liamlacey/Vintage-Toy-Synthesiser/Code/RPi/VintageToySynthProject/VintageSoundEngine/Maximilian/maximilian.cpp

/*
 *  maximilian.cpp
 *  platform independent synthesis library using portaudio or rtaudio
 *
 *  Created by Mick Grierson on 29/12/2009.
 *  Copyright 2009 Mick Grierson & Strangeloop Limited. All rights reserved.
 *	Thanks to the Goldsmiths Creative Computing Team.
 *	Special thanks to Arturo Castro for the PortAudio implementation.
 *
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
 */

#include "maximilian.h"
#include "math.h"

/*  Maximilian can be configured to load ogg vorbis format files using the 
*   loadOgg() method.
*   Uncomment the following to include Sean Barrett's Ogg Vorbis decoder.
*   If you're on windows, make sure to add the files std_vorbis.c and std_vorbis.h to your project*/

//#define VORBIS

#ifdef VORBIS
extern "C" {
    #include "stb_vorbis.h"
}
#endif

//This used to be important for dealing with multichannel playback
float chandiv= 1;

int maxiSettings::sampleRate = 44100;
int maxiSettings::channels = 2;
//int maxiSettings::bufferSize = 1024;
int maxiSettings::bufferSize = 128;

//this is a 514-point sinewave table that has many uses. 
double sineBuffer[514]={0,0.012268,0.024536,0.036804,0.049042,0.06131,0.073547,0.085785,0.097992,0.1102,0.12241,0.13455,0.1467,0.15884,0.17093,0.18301,0.19507,0.20709,0.21909,0.23105,0.24295,0.25485,0.26669,0.2785,0.29025,0.30197,0.31366,0.32529,0.33685,0.34839,0.35986,0.37128,0.38266,0.39395,0.40521,0.41641,0.42752,0.4386,0.44958,0.46051,0.47137,0.48215,0.49286,0.50351,0.51407,0.52457,0.53497,0.54529,0.55554,0.5657,0.57578,0.58575,0.59567,0.60547,0.6152,0.62482,0.63437,0.6438,0.65314,0.66238,0.67151,0.68057,0.68951,0.69833,0.70706,0.7157,0.72421,0.7326,0.74091,0.74908,0.75717,0.76514,0.77298,0.7807,0.7883,0.79581,0.80316,0.81042,0.81754,0.82455,0.83142,0.8382,0.84482,0.85132,0.8577,0.86392,0.87006,0.87604,0.88187,0.8876,0.89319,0.89862,0.90396,0.90912,0.91415,0.91907,0.92383,0.92847,0.93295,0.93729,0.9415,0.94556,0.94949,0.95325,0.95691,0.96039,0.96375,0.96692,0.97,0.9729,0.97565,0.97827,0.98074,0.98306,0.98523,0.98724,0.98914,0.99084,0.99243,0.99387,0.99515,0.99628,0.99725,0.99808,0.99875,0.99927,0.99966,0.99988,0.99997,0.99988,0.99966,0.99927,0.99875,0.99808,0.99725,0.99628,0.99515,0.99387,0.99243,0.99084,0.98914,0.98724,0.98523,0.98306,0.98074,0.97827,0.97565,0.9729,0.97,0.96692,0.96375,0.96039,0.95691,0.95325,0.94949,0.94556,0.9415,0.93729,0.93295,0.92847,0.92383,0.91907,0.91415,0.90912,0.90396,0.89862,0.89319,0.8876,0.88187,0.87604,0.87006,0.86392,0.8577,0.85132,0.84482,0.8382,0.83142,0.82455,0.81754,0.81042,0.80316,0.79581,0.7883,0.7807,0.77298,0.76514,0.75717,0.74908,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
	phase=phaseIn;
	
}

double maxiOsc::sinewave(double frequency) {
    //This is a sinewave oscillator
	output=sin (phase*(TWOPI));
	if ( phase >= 1.0 ) phase -= 1.0;
	phase += (1./(maxiSettings::sampleRate/(frequency)));
	return(output);
	
}

double maxiOsc::sinebuf4(double frequency) {
    //This is a sinewave oscillator that uses 4 point interpolation on a 514 point buffer
	double remainder;
	double a,b,c,d,a1,a2,a3;
	phase += 512./(maxiSettings::sampleRate/(frequency));
	if ( phase >= 511 ) phase -=512;
	remainder = phase - floor(phase);
	
	if (phase==0) {
		a=sineBuffer[(long) 512];
		b=sineBuffer[(long) phase];
		c=sineBuffer[(long) phase+1];
		d=sineBuffer[(long) phase+2];
		
	} else {
		a=sineBuffer[(long) phase-1];
		b=sineBuffer[(long) phase];
		c=sineBuffer[(long) phase+1];
		d=sineBuffer[(long) phase+2];
		
	}
	
	a1 = 0.5f * (c - a);
	a2 = a - 2.5 * b + 2.f * c - 0.5f * d;
	a3 = 0.5f * (d - a) + 1.5f * (b - c);
	output = double (((a3 * remainder + a2) * remainder + a1) * remainder + b);
	return(output);
}

double maxiOsc::sinebuf(double frequency) { //specify the frequency of the oscillator in Hz / cps etc.
    //This is a sinewave oscillator that uses linear interpolation on a 514 point buffer
	double remainder;
 	phase += 512./(maxiSettings::sampleRate/(frequency*chandiv));
	if ( phase >= 511 ) phase -=512;
	remainder = phase - floor(phase);
	output = (double) ((1-remainder) * sineBuffer[1+ (long) phase] + remainder * sineBuffer[2+(long) phase]);
	return(output);
}

double maxiOsc::coswave(double frequency) {
    //This is a cosine oscillator
	output=cos (phase*(TWOPI));
	if ( phase >= 1.0 ) phase -= 1.0;
	phase += (1./(maxiSettings::sampleRate/(frequency)));
	return(output);
	
}

double maxiOsc::phasor(double frequency) {
    //This produces a floating point linear ramp between 0 and 1 at the desired frequency 
	output=phase;
	if ( phase >= 1.0 ) phase -= 1.0;
	phase += (1./(maxiSettings::sampleRate/(frequency)));
	return(output);
} 

double maxiOsc::square(double frequency) {
    //This is a square wave
	if (phase<0.5) output=-1;
	if (phase>0.5) output=1;
	if ( phase >= 1.0 ) phase -= 1.0;
	phase += (1./(maxiSettings::sampleRate/(frequency)));
	return(output);
}

double maxiOsc::pulse(double frequency, double duty) {
    //This is a pulse generator that creates a signal between -1 and 1.
	if (duty<0.) duty=0;
	if (duty>1.) duty=1;
	if ( phase >= 1.0 ) phase -= 1.0;
	phase += (1./(maxiSettings::sampleRate/(frequency)));
	if (phase<duty) output=-1.;
	if (phase>duty) output=1.;
	return(output);
}

double maxiOsc::phasor(double frequency, double startphase, double endphase) {
    //This is a phasor that takes a value for the start and end of the ramp. 
	output=phase;
	if (phase<startphase) {
		phase=startphase;
	}
	if ( phase >= endphase ) phase = startphase;
	phase += ((endphase-startphase)/(maxiSettings::sampleRate/(frequency)));
	return(output);
}


double maxiOsc::saw(double frequency) {
	//Sawtooth generator. This is like a phasor but goes between -1 and 1
	output=phase;
	if ( phase >= 1.0 ) phase -= 2.0;
	phase += (1./(maxiSettings::sampleRate/(frequency)));
	return(output);
	
}

double maxiOsc::sawn(double frequency) {
	//Bandlimited sawtooth generator. Woohoo.
    if ( phase >= 0.5 ) phase -= 1.0;
    phase += (1./(maxiSettings::sampleRate/(frequency)));
	double temp=(8820.22/frequency)*phase;
    if (temp<-0.5) {
        temp=-0.5;
    }
    if (temp>0.5) {
        temp=0.5;
    }
    temp*=1000.0f;
    temp+=500.0f;
    double remainder = temp - floor(temp);
    output = (double) ((1.0f-remainder) * transition[(long)temp] + remainder * transition[1+(long)temp]) - phase;
	return(output);
	
}

double maxiOsc::rect(double frequency, double duty) {

    return (output);
}

double maxiOsc::triangle(double frequency) {
    //This is a triangle wave.
	if ( phase >= 1.0 ) phase -= 1.0;
	phase += (1./(maxiSettings::sampleRate/(frequency)));
	if (phase <= 0.5 ) {
		output =(phase - 0.25) * 4;
	} else {
		output =((1.0-phase) - 0.25) * 4;
	}
	return(output);
	
}

double maxiEnvelope::line(int numberofsegments,double segments[1000]) {
	//This is a basic multi-segment ramp generator that you can use for more or less anything.
    //However, it's not that intuitive.
    if (isPlaying==1) {//only make a sound once you've been triggered
	period=4./(segments[valindex+1]*0.0044);
	nextval=segments[valindex+2];
	currentval=segments[valindex];
	if (currentval-amplitude > 0.0000001 && valindex < numberofsegments) {
		amplitude += ((currentval-startval)/(maxiSettings::sampleRate/period));
	} else if (currentval-amplitude < -0.0000001 && valindex < numberofsegments) {
		amplitude -= (((currentval-startval)*(-1))/(maxiSettings::sampleRate/period));
	} else if (valindex >numberofsegments-1) {
		valindex=numberofsegments-2;
	} else {
		valindex=valindex+2;
		startval=currentval;
	}
	output=amplitude;
		
	}
	else {
		output=0;
		
	}
	return(output);
}

//and this
void maxiEnvelope::trigger(int index, double amp) {
	isPlaying=1;//ok the envelope is being used now.
	valindex=index;
	amplitude=amp;
	
}

//Delay with feedback
maxiDelayline::maxiDelayline() {
	memset( memory, 0, 88200*sizeof (double) );	
}


double maxiDelayline::dl(double input, int size, double feedback)  {
	if ( phase >=size ) {
		phase = 0;
	}
	output=memory[phase];
	memory[phase]=(memory[phase]*feedback)+(input*feedback)*0.5;
	phase+=1;
	return(output);
	
}

double maxiDelayline::dl(double input, int size, double feedback, int position)  {
	if ( phase >=size ) phase = 0;
	if ( position >=size ) position = 0;
	output=memory[position];
	memory[phase]=(memory[phase]*feedback)+(input*feedback)*chandiv;
	phase+=1;
	return(output);
	
}

//I particularly like these. cutoff between 0 and 1
double maxiFilter::lopass(double input, double cutoff) {
	output=outputs[0] + cutoff*(input-outputs[0]);
	outputs[0]=output;
	return(output);
}

//as above
double maxiFilter::hipass(double input, double cutoff) {
	output=input-(outputs[0] + cutoff*(input-outputs[0]));
	outputs[0]=output;
	return(output);
}
//awesome. cuttof is freq in hz. res is between 1 and whatever. Watch out!
double maxiFilter::lores(double input,double cutoff1, double resonance) {
	cutoff=cutoff1;
	if (cutoff<10) cutoff=10;
	if (cutoff>(maxiSettings::sampleRate)) cutoff=(maxiSettings::sampleRate);
	if (resonance<1.) resonance = 1.;
	z=cos(TWOPI*cutoff/maxiSettings::sampleRate);
	c=2-2*z;
	double r=(sqrt(2.0)*sqrt(-pow((z-1.0),3.0))+resonance*(z-1))/(resonance*(z-1));
	x=x+(input-y)*c;
	y=y+x;
	x=x*r;
	output=y;
	return(output);
}

//working hires filter
double maxiFilter::hires(double input,double cutoff1, double resonance) {
	cutoff=cutoff1;
	if (cutoff<10) cutoff=10;
	if (cutoff>(maxiSettings::sampleRate)) cutoff=(maxiSettings::sampleRate);
	if (resonance<1.) resonance = 1.;
	z=cos(TWOPI*cutoff/maxiSettings::sampleRate);
	c=2-2*z;
	double r=(sqrt(2.0)*sqrt(-pow((z-1.0),3.0))+resonance*(z-1))/(resonance*(z-1));
	x=x+(input-y)*c;
	y=y+x;
	x=x*r;
	output=input-y;
	return(output);
}

//This works a bit. Needs attention.
double maxiFilter::bandpass(double input,double cutoff1, double resonance) {
	cutoff=cutoff1;
	if (cutoff>(maxiSettings::sampleRate*0.5)) cutoff=(maxiSettings::sampleRate*0.5);
	if (resonance>=1.) resonance=0.999999;
	z=cos(TWOPI*cutoff/maxiSettings::sampleRate);
	inputs[0] = (1-resonance)*(sqrt(resonance*(resonance-4.0*pow(z,2.0)+2.0)+1));
	inputs[1] = 2*z*resonance;
	inputs[2] = pow((resonance*-1),2);
	
	output=inputs[0]*input+inputs[1]*outputs[1]+inputs[2]*outputs[2];
	outputs[2]=outputs[1];
	outputs[1]=output;
	return(output);
}

//stereo bus
double *maxiMix::stereo(double input,double two[2],double x) {
	if (x>1) x=1;
	if (x<0) x=0;
	two[0]=input*sqrt(1.0-x);
	two[1]=input*sqrt(x);
	return(two);
} 

//quad bus
double *maxiMix::quad(double input,double four[4],double x,double y) {
	if (x>1) x=1;
	if (x<0) x=0;
	if (y>1) y=1;
	if (y<0) y=0;
	four[0]=input*sqrt((1.0-x)*y);
	four[1]=input*sqrt((1.0-x)*(1.0-y));
	four[2]=input*sqrt(x*y);
	four[3]=input*sqrt(x*(1.0-y));
	return(four);
}

//ambisonic bus
double *maxiMix::ambisonic(double input,double eight[8],double x,double y,double z) {
	if (x>1) x=1;
	if (x<0) x=0;
	if (y>1) y=1;
	if (y<0) y=0;
	if (z>1) y=1;
	if (z<0) y=0;
	eight[0]=input*(sqrt((1.0-x)*y)*1.0-z);
	eight[1]=input*(sqrt((1.0-x)*(1.0-y))*1.0-z);
	eight[2]=input*(sqrt(x*y)*1.0-z);
	eight[3]=input*(sqrt(x*(1.0-y))*1.0-z);
	eight[4]=input*(sqrt((1.0-x)*y)*z);
	eight[5]=input*(sqrt((1.0-x)*(1.0-y))*z);
	eight[6]=input*sqrt((x*y)*z);
	eight[7]=input*sqrt((x*(1.0-y))*z);
	return(eight);
}

//This is the maxiSample load function. It just calls read.
bool maxiSample::load(string fileName, int channel) {
	myPath = fileName;
	readChannel=channel;
	return read();
}

// This is for OGG loading
bool maxiSample::loadOgg(string fileName, int channel) {
#ifdef VORBIS
    bool result;
	readChannel=channel;
    int channelx;
//    cout << fileName << endl;
    free(temp);
    myDataSize = stb_vorbis_decode_filename(const_cast<char*>(fileName.c_str()), &channelx, &temp);
    result = myDataSize > 0;
    printf("\nchannels = %d\nlength = %d",channelx,myDataSize);
    printf("\n");
    myChannels=(short)channelx;
    length=myDataSize;
    mySampleRate=44100;
    
    if (myChannels>1) {
        int position=0;
        int channel=readChannel;
        for (int i=channel;i<myDataSize*2;i+=myChannels) {
            temp[position]=temp[i];
            position++;
        }
    }
	return result; // this should probably be something more descriptive
#endif
    return 0;
}

//This sets the playback position to the start of a sample
void maxiSample::trigger() {
	position = 0;
    recordPosition = 0;
}

//This is the main read function.
bool maxiSample::read()
{
	bool result;
	ifstream inFile( myPath.c_str(), ios::in | ios::binary);
	result = inFile.is_open();
	if (result) {
		bool datafound = false;
		inFile.seekg(4, ios::beg);
		inFile.read( (char*) &myChunkSize, 4 ); // read the ChunkSize
		
		inFile.seekg(16, ios::beg);
		inFile.read( (char*) &mySubChunk1Size, 4 ); // read the SubChunk1Size
		
		//inFile.seekg(20, ios::beg);
		inFile.read( (char*) &myFormat, sizeof(short) ); // read the file format.  This should be 1 for PCM
		
		//inFile.seekg(22, ios::beg);
		inFile.read( (char*) &myChannels, sizeof(short) ); // read the # of channels (1 or 2)
		
		//inFile.seekg(24, ios::beg);
		inFile.read( (char*) &mySampleRate, sizeof(int) ); // read the samplerate
		
		//inFile.seekg(28, ios::beg);
		inFile.read( (char*) &myByteRate, sizeof(int) ); // read the byterate
		
		//inFile.seekg(32, ios::beg);
		inFile.read( (char*) &myBlockAlign, sizeof(short) ); // read the blockalign
		
		//inFile.seekg(34, ios::beg);
		inFile.read( (char*) &myBitsPerSample, sizeof(short) ); // read the bitspersample
		
		//ignore any extra chunks
		char chunkID[5]="";
		chunkID[4] = 0;
		int filePos = 20 + mySubChunk1Size;
		while(!datafound && !inFile.eof()) {
			inFile.seekg(filePos, ios::beg);
			inFile.read((char*) &chunkID, sizeof(char) * 4);
			inFile.seekg(filePos + 4, ios::beg);
			inFile.read( (char*) &myDataSize, sizeof(int) ); // read the size of the data
			filePos += 8;
			if (strcmp(chunkID,"data") == 0) {
				datafound = true;
			}else{
				filePos += myDataSize;
			}
		}
		
		// read the data chunk
		char * myData = (char*) malloc(myDataSize * sizeof(char));
		inFile.seekg(filePos, ios::beg);
		inFile.read(myData, myDataSize);
		length=myDataSize*(0.5/myChannels);
		inFile.close(); // close the input file
		
        cout << "Ch: " << myChannels << ", len: " << length << endl;
		if (myChannels>1) {
			int position=0;
			int channel=readChannel*2;
			for (int i=channel;i<myDataSize+6;i+=(myChannels*2)) {
				myData[position]=myData[i];
				myData[position+1]=myData[i+1];
				position+=2;
			}
		}
        free(temp);
        temp = (short*) malloc(myDataSize * sizeof(char));
        memcpy(temp, myData, myDataSize * sizeof(char));
        
        free(myData);
		
	}else {
//		cout << "ERROR: Could not load sample: " <<myPath << endl; //This line seems to be hated by windows 
        printf("ERROR: Could not load sample.");

	}
	
	
	return result; // this should probably be something more descriptive
}

//This plays back at the correct speed. Always loops.
double maxiSample::play() {
	position++;
	if ((long) position >= length) position=0;
	output = (double) temp[(long)position]/32767.0;
	return output;
}

void maxiSample::setPosition(double newPos) {
    position = maxiMap::clamp<double>(newPos, 0.0, 1.0) * length;
}

//start end and points are between 0 and 1
double maxiSample::playLoop(double start, double end) {
    position++;
    if (position < length * start) position = length * start;
    if ((long) position >= length * end) position = length * start;
    output = (double) temp[(long)position]/32767.0;
    return output;
}

double maxiSample::playUntil(double end) {
    position++;
    if ((long) position<length * end)
        output = (double) temp[(long)position]/32767.0;
    else {
        output=0;
    }
    return output;
}


//This plays back at the correct speed. Only plays once. To retrigger, you have to manually reset the position
double maxiSample::playOnce() {
	position++;
	if ((long) position<length)
        output = (double) temp[(long)position]/32767.0;
    else {
        output=0;
    }
	return output;

}

//Same as above but takes a speed value specified as a ratio, with 1.0 as original speed
double maxiSample::playOnce(double speed) {
	position=position+((speed*chandiv)/(maxiSettings::sampleRate/mySampleRate));
	double remainder = position - (long) position;
	if ((long) position<length)
		output = (double) ((1-remainder) * temp[1+ (long) position] + remainder * temp[2+(long) position])/32767;//linear interpolation
	else 
		output=0;
	return(output);
}

//As above but looping
double maxiSample::play(double speed) {
	double remainder;
	long a,b;
	position=position+((speed*chandiv)/(maxiSettings::sampleRate/mySampleRate));
	if (speed >=0) {
		
		if ((long) position>=length-1) position=1;
		remainder = position - floor(position);
		if (position+1<length) {
			a=position+1;
			
		}
		else {
			a=length-1;
		}
		if (position+2<length)
		{
		b=position+2;
		}
		else {
		b=length-1;
		}
		
		output = (double) ((1-remainder) * temp[a] + remainder * temp[b])/32767;//linear interpolation
} else {
		if ((long) position<0) position=length;
		remainder = position - floor(position);
		if (position-1>=0) {
			a=position-1;
				
			}
			else {
				a=0;
			}
	if (position-2>=0) {
		b=position-2;
			}
			else {
				b=0;
			}
		output = (double) ((-1-remainder) * temp[a] + remainder * temp[b])/32767;//linear interpolation
	}	
	return(output);
}

//placeholder
double maxiSample::play(double frequency, double start, double end) {
	return play(frequency, start, end, position);
}

//This allows you to say how often a second you want a specific chunk of audio to play
double maxiSample::play(double frequency, double start, double end, double &pos) {
	double remainder;
	if (end>=length) end=length-1;
	long a,b;

	if (frequency >0.) {
		if (pos<start) {
			pos=start;
		}
		
		if ( pos >= end ) pos = start;
		pos += ((end-start)/((maxiSettings::sampleRate)/(frequency*chandiv)));
		remainder = pos - floor(pos);
		long posl = floor(pos);
		if (posl+1<length) {
			a=posl+1;
			
		}
		else {
			a=posl-1;
		}
		if (posl+2<length) {
			b=posl+2;
		}
		else {
			b=length-1;
		}

		output = (double) ((1-remainder) * temp[a] +
						   remainder * temp[b])/32767;//linear interpolation
	} else {
		frequency*=-1.;
		if ( pos <= start ) pos = end;
		pos -= ((end-start)/(maxiSettings::sampleRate/(frequency*chandiv)));
		remainder = pos - floor(pos);
		long posl = floor(pos);
		if (posl-1>=0) {
			a=posl-1;
		}
		else {
			a=0;
		}
		if (posl-2>=0) {
			b=posl-2;
		}
		else {
			b=0;
		}		
		output = (double) ((-1-remainder) * temp[a] +
						   remainder * temp[b])/32767;//linear interpolation
		
	}
	
	return(output);
}


//Same as above. better cubic inerpolation. Cobbled together from various (pd externals, yehar, other places).
double maxiSample::play4(double frequency, double start, double end) {
	double remainder;
	double a,b,c,d,a1,a2,a3;
	if (frequency >0.) {
		if (position<start) {
			position=start;
		}
		if ( position >= end ) position = start;
		position += ((end-start)/(maxiSettings::sampleRate/(frequency*chandiv)));
		remainder = position - floor(position);
		if (position>0) {
			a=temp[(int)(floor(position))-1];

		} else {
			a=temp[0];
			
		}
		
		b=temp[(long) position];
		if (position<end-2) {
			c=temp[(long) position+1];

		} else {
			c=temp[0];

		}
		if (position<end-3) {
			d=temp[(long) position+2];

		} else {
			d=temp[0];
		}
		a1 = 0.5f * (c - a);
		a2 = a - 2.5 * b + 2.f * c - 0.5f * d;
		a3 = 0.5f * (d - a) + 1.5f * (b - c);
		output = (double) (((a3 * remainder + a2) * remainder + a1) * remainder + b) / 32767;
		
	} else {
        frequency*=-1.;
		if ( position <= start ) position = end;
		position -= ((end-start)/(maxiSettings::sampleRate/(frequency*chandiv)));
		remainder = position - floor(position);
		if (position>start && position < end-1) {
			a=temp[(long) position+1];
			
		} else {
			a=temp[0];
			
		}
		
		b=temp[(long) position];
		if (position>start) {
			c=temp[(long) position-1];
			
		} else {
			c=temp[0];
			
		}
		if (position>start+1) {
			d=temp[(long) position-2];
			
		} else {
			d=temp[0];
		}
		a1 = 0.5f * (c - a);
		a2 = a - 2.5 * b + 2.f * c - 0.5f * d;
		a3 = 0.5f * (d - a) + 1.5f * (b - c);
		output = (double) (((a3 * remainder + a2) * -remainder + a1) * -remainder + b) / 32767;
		
	}
	
	return(output);
}


//You don't need to worry about this stuff.
double maxiSample::bufferPlay(unsigned char &bufferin,long length) {
	double remainder;
	short* buffer = (short *)&bufferin;
	position=(position+1);
	remainder = position - (long) position;
	if ((long) position>length) position=0;
	output = (double) ((1-remainder) * buffer[1+ (long) position] + remainder * buffer[2+(long) position])/32767;//linear interpolation
	return(output);
}

double maxiSample::bufferPlay(unsigned char &bufferin,double speed,long length) {
	double remainder;
	long a,b;
	short* buffer = (short *)&bufferin;
	position=position+((speed*chandiv)/(maxiSettings::sampleRate/mySampleRate));
	if (speed >=0) {
		
		if ((long) position>=length-1) position=1;
		remainder = position - floor(position);
		if (position+1<length) {
			a=position+1;
			
		}
		else {
			a=length-1;
		}
		if (position+2<length)
		{
			b=position+2;
		}
		else {
			b=length-1;
		}
		
		output = (double) ((1-remainder) * buffer[a] + remainder * buffer[b])/32767;//linear interpolation
	} else {
		if ((long) position<0) position=length;
		remainder = position - floor(position);
		if (position-1>=0) {
			a=position-1;
			
		}
		else {
			a=0;
		}
		if (position-2>=0) {
			b=position-2;
		}
		else {
			b=0;
		}
		output = (double) ((-1-remainder) * buffer[a] + remainder * buffer[b])/32767;//linear interpolation
	}	
	return(output);
}

double maxiSample::bufferPlay(unsigned char &bufferin,double frequency, double start, double end) {
	double remainder;
	length=end;
	long a,b;
	short* buffer = (short *)&bufferin;
	if (frequency >0.) {
		if (position<start) {
			position=start;
		}
		
		if ( position >= end ) position = start;
		position += ((end-start)/(maxiSettings::sampleRate/(frequency*chandiv)));
		remainder = position - floor(position);
		long pos = floor(position);
		if (pos+1<length) {
			a=pos+1;
			
		}
		else {
			a=pos-1;
		}
		if (pos+2<length) {
			b=pos+2;
		}
		else {
			b=length-1;
		}
		
		output = (double) ((1-remainder) * buffer[a] +
						   remainder * buffer[b])/32767;//linear interpolation
	} else {
        frequency*=-1.;
		if ( position <= start ) position = end;
		position -= ((end-start)/(maxiSettings::sampleRate/(frequency*chandiv)));
		remainder = position - floor(position);
		long pos = floor(position);
		if (pos-1>=0) {
			a=pos-1;
		}
		else {
			a=0;
		}
		if (pos-2>=0) {
			b=pos-2;
		}
		else {
			b=0;
		}		
		output = (double) ((-1-remainder) * buffer[a] +
						   remainder * buffer[b])/32767;//linear interpolation
		
	}
	
	return(output);
}

//better cubic inerpolation. Cobbled together from various (pd externals, yehar, other places).
double maxiSample::bufferPlay4(unsigned char &bufferin,double frequency, double start, double end) {
	double remainder;
	double a,b,c,d,a1,a2,a3;
	short* buffer = (short*)&bufferin;
	if (frequency >0.) {
		if (position<start) {
			position=start;
		}
		if ( position >= end ) position = start;
		position += ((end-start)/(maxiSettings::sampleRate/(frequency*chandiv)));
		remainder = position - floor(position);
		if (position>0) {
			a=buffer[(int)(floor(position))-1];
			
		} else {
			a=buffer[0];
			
		}
		
		b=buffer[(long) position];
		if (position<end-2) {
			c=buffer[(long) position+1];
			
		} else {
			c=buffer[0];
			
		}
		if (position<end-3) {
			d=buffer[(long) position+2];
			
		} else {
			d=buffer[0];
		}
		a1 = 0.5f * (c - a);
		a2 = a - 2.5 * b + 2.f * c - 0.5f * d;
		a3 = 0.5f * (d - a) + 1.5f * (b - c);
		output = (double) (((a3 * remainder + a2) * remainder + a1) * remainder + b) / 32767;
		
	} else {
        frequency*=-1.;
		if ( position <= start ) position = end;
		position -= ((end-start)/(maxiSettings::sampleRate/(frequency*chandiv)));
		remainder = position - floor(position);
		if (position>start && position < end-1) {
			a=buffer[(long) position+1];
			
		} else {
			a=buffer[0];
			
		}
		
		b=buffer[(long) position];
		if (position>start) {
			c=buffer[(long) position-1];
			
		} else {
			c=buffer[0];
			
		}
		if (position>start+1) {
			d=buffer[(long) position-2];
			
		} else {
			d=buffer[0];
		}
		a1 = 0.5f * (c - a);
		a2 = a - 2.5 * b + 2.f * c - 0.5f * d;
		a3 = 0.5f * (d - a) + 1.5f * (b - c);
		output = (double) (((a3 * remainder + a2) * -remainder + a1) * -remainder + b) / 32767;
		
	}
	
	return(output);
}


void maxiSample::getLength() {
	length=myDataSize*0.5;
}

void maxiSample::setLength(unsigned long numSamples) {
    cout << "Length: " << numSamples << endl;
    short *newData = (short*) malloc(sizeof(short) * numSamples);
    if (NULL!=temp) {
        unsigned long copyLength = min((unsigned long)length, numSamples);
        memcpy(newData, temp, sizeof(short) * copyLength);
    }
    temp = newData;
    myDataSize = numSamples * 2;
    length=numSamples;
    position=0;
    recordPosition=0;
}

void maxiSample::clear() {
    memset(temp, 0, myDataSize);
}

void maxiSample::reset() {
    position=0;
}

void maxiSample::normalise(float maxLevel) {
    short maxValue = 0;
    for(int i=0; i < length; i++) {
        if (abs(temp[i]) > maxValue) {
            maxValue = abs(temp[i]);
        }
    }
    float scale = 32767.0 * maxLevel / (float) maxValue;
    for(int i=0; i < length; i++) {
        temp[i] = round(scale * (float) temp[i]);
    }
}

void maxiSample::autoTrim(float alpha, float threshold, bool trimStart, bool trimEnd) {
    
    int startMarker=0;
    if(trimStart) {
        maxiLagExp<float> startLag(alpha, 0);
        while(startMarker < length) {
            startLag.addSample(abs(temp[startMarker]));
            if (startLag.value() > threshold) {
                break;
            }
            startMarker++;
        }
    }
    
    int endMarker = length-1;
    if(trimEnd) {
        maxiLagExp<float> endLag(alpha, 0);
        while(endMarker > 0) {
            endLag.addSample(abs(temp[endMarker]));
            if (endLag.value() > threshold) {
                break;
            }
            endMarker--;
        }
    }
    
    cout << "Autotrim: start: " << startMarker << ", end: " << endMarker << endl;
    
    int newLength = endMarker - startMarker;
    if (newLength > 0) {
        short *newData = (short*) malloc(sizeof(short) * newLength);
        for(int i=0; i < newLength; i++) {
            newData[i] = temp[i+startMarker];
        }
        free(temp);
        temp = newData;
        myDataSize = newLength * 2;
        length=newLength;
        position=0;
        recordPosition=0;
        //envelope the start
        int fadeSize=min((long)100, length);
        for(int i=0; i < fadeSize; i++) {
            float factor = i / (float) fadeSize;
            temp[i] = round(temp[i] * factor);
            temp[length - 1 - i] = round(temp[length - 1 - i] * factor);
        }
    }
}





/* OK this compressor and gate are now ready to use. The envelopes, like all the envelopes in this recent update, use stupid algorithms for 
 incrementing - consequently a long attack is something like 0.0001 and a long release is like 0.9999.
 Annoyingly, a short attack is 0.1, and a short release is 0.99. I'll sort this out laters */

double maxiDyn::gate(double input, double threshold, long holdtime, double attack, double release) {
	
	if (fabs(input)>threshold && attackphase!=1){ 
		holdcount=0;
		releasephase=0;
		attackphase=1;
		if(amplitude==0) amplitude=0.01;
	}
	
	if (attackphase==1 && amplitude<1) {
		amplitude*=(1+attack);
		output=input*amplitude;
	}
	
	if (amplitude>=1) {
		attackphase=0;
		holdphase=1;
	}
	
	if (holdcount<holdtime && holdphase==1) {
		output=input;
		holdcount++;
	}
	
	if (holdcount==holdtime) {
		holdphase=0;
		releasephase=1;
	}
	
	if (releasephase==1 && amplitude>0.) {
		output=input*(amplitude*=release);
		
	}
	
	return output;
}


double maxiDyn::compressor(double input, double ratio, double threshold, double attack, double release) {
	
	if (fabs(input)>threshold && attackphase!=1){ 
		holdcount=0;
		releasephase=0;
		attackphase=1;
		if(currentRatio==0) currentRatio=ratio;
	}
	
	if (attackphase==1 && currentRatio<ratio-1) {
		currentRatio*=(1+attack);
	}
	
	if (currentRatio>=ratio-1) {
		attackphase=0;
		releasephase=1;
	}
	
	if (releasephase==1 && currentRatio>0.) {
		currentRatio*=release;		
	}
	
	if (input>0.) {
		output = input/(1.+currentRatio);
	} else {
		output = input/(1.+currentRatio);
	}
	
	return output*(1+log(ratio));
}

double maxiDyn::compress(double input) {
    
    if (fabs(input)>threshold && attackphase!=1){
        holdcount=0;
        releasephase=0;
        attackphase=1;
        if(currentRatio==0) currentRatio=ratio;
    }
    
    if (attackphase==1 && currentRatio<ratio-1) {
        currentRatio*=(1+attack);
    }
    
    if (currentRatio>=ratio-1) {
        attackphase=0;
        releasephase=1;
    }
    
    if (releasephase==1 && currentRatio>0.) {
        currentRatio*=release;
    }
    
    if (input>0.) {
        output = input/(1.+currentRatio);
    } else {
        output = input/(1.+currentRatio);
    }
    
    return output*(1+log(ratio));
}


//ltml - added by me
maxiEnv::maxiEnv()
{
    holdtime = 1;
}

/* Lots of people struggle with the envelope generators so here's a new easy one.
 It takes mental numbers for attack and release tho. Basically, they're exponentials.
 I'll map them out later so that it's a bit more intuitive */
double maxiEnv::ar(double input, double attack, double release, long holdtime, int trigger) {
	
	if (trigger==1 && attackphase!=1 && holdphase!=1){ 
		holdcount=0;
		releasephase=0;
		attackphase=1;
	}
	
	if (attackphase==1) {
		amplitude+=(1*attack);
		output=input*amplitude;
	}
	
	if (amplitude>=1) {
		amplitude=1;
		attackphase=0;
		holdphase=1;
	}
	
	if (holdcount<holdtime && holdphase==1) {
		output=input;
		holdcount++;
	}
	
	if (holdcount==holdtime && trigger==1) {
		output=input;
	}
	
	if (holdcount==holdtime && trigger!=1) {
		holdphase=0;
		releasephase=1;
	}
	
	if (releasephase==1 && amplitude>0.) {
		output=input*(amplitude*=release);
		
	}
	
	return output;
}

/* adsr. It's not bad, very simple to use*/

double maxiEnv::adsr(double input, double attack, double decay, double sustain, double release, long holdtime, int trigger) {
    
    if (trigger==1 && attackphase!=1 && holdphase!=1 && decayphase!=1){
        holdcount=0;
        decayphase=0;
        sustainphase=0;
        releasephase=0;
        attackphase=1;
    }
    
    if (attackphase==1) {
        releasephase=0;
        amplitude+=(1*attack);
        output=input*amplitude;
        
        if (amplitude>=1) {
            amplitude=1;
            attackphase=0;
            decayphase=1;
        }
    }
    
    
    if (decayphase==1) {
        output=input*(amplitude*=decay);
        if (amplitude<=sustain) {
            decayphase=0;
            holdphase=1;
        }
    }
    
    if (holdcount<holdtime && holdphase==1) {
        output=input*amplitude;
        holdcount++;
    }
    
    if (holdcount>=holdtime && trigger==1) {
        output=input*amplitude;
    }
    
    if (holdcount>=holdtime && trigger!=1) {
        holdphase=0;
        releasephase=1;
    }
    
    if (releasephase==1 && amplitude>0.) {
        output=input*(amplitude*=release);
        
    }
    
    return output;
}

double maxiEnv::adsr(double input, int trigger)
{
    //if get a trigger value of 1 while in no phase or the release phase
    if (trigger == 1 && attackphase != 1 && sustainphase != 1 && decayphase != 1)
    {
        //reset variables and start the attack phase
        decayphase = 0;
        sustainphase = 0;
        releasephase = 0;
        attackphase = 1;
    }
    
    //if get a trigger value of 0 while in the attack, decay, or sustain ohase
    else if (trigger == 0 && (attackphase == 1 || decayphase == 1 || sustainphase == 1))
    {
        //start the release phase
        attackphase = 0;
        decayphase = 0;
        sustainphase = 0;
        releasephase = 1;
    }
    
    //if in the attack phase
    if (attackphase == 1 && trigger == 1)
    {
        //increment the output value
        amplitude += (1 * attack);
        output = input * amplitude;
        
        //if reached the end of the attack phase
        if (amplitude >= 1)
        {
            amplitude = 1;
            attackphase = 0;
            
            //if we have a decay time
            if (decay > 0)
            {
                //start the decay phase
                decayphase = 1;
            }
            //if decay time is set to 0
            else
            {
                //start the sustain phase
                amplitude = sustain;
                sustainphase = 1;
            }
            
        } //if (amplitude >= 1)
        
    } //if (attackphase == 1 && trigger == 1)
    
    //if in the decay phase
    if (decayphase == 1 && trigger == 1)
    {
        //increment the output value
        output = input * (amplitude *= decay);
        
        //if reached the start of the sustain phase
        if (amplitude <= sustain)
        {
            //start the sustain phase
            decayphase = 0;
            sustainphase = 1;
        }
    }
    
    //if in the sustain phase
    if (sustainphase == 1 && trigger == 1)
    {
        //keep the output value at the sustain value
        output = input * amplitude;
    }
    
    //if in the release phase
    if (releasephase == 1 && amplitude > 0.)
    {
        //increment the output value
        output = input * (amplitude *= release);
    }
    
    return output;
    
    
//    if (trigger==1 && attackphase!=1 && holdphase!=1 && decayphase!=1){
//        holdcount=0;
//        decayphase=0;
//        sustainphase=0;
//        releasephase=0;
//        attackphase=1;
//    }
//    
//    if (attackphase==1) {
//        releasephase=0;
//        amplitude+=(1*attack);
//        output=input*amplitude;
//        
//        if (amplitude>=1) {
//            amplitude=1;
//            attackphase=0;
//            decayphase=1;
//        }
//    }
//    
//    
//    if (decayphase==1) {
//        output=input*(amplitude*=decay);
//        if (amplitude<=sustain) {
//            decayphase=0;
//            holdphase=1;
//        }
//    }
//    
//    if (holdcount<holdtime && holdphase==1) {
//        output=input*amplitude;
//        holdcount++;
//    }
//    
//    if (holdcount>=holdtime && trigger==1) {
//        output=input*amplitude;
//    }
//    
//    if (holdcount>=holdtime && trigger!=1) {
//        holdphase=0;
//        releasephase=1;
//    }
//    
//    if (releasephase==1 && amplitude>0.) {
//        output=input*(amplitude*=release);
//        
//    }
//    
//    return output;
}


void maxiEnv::setAttack(double attackMS) {
    attack = 1-pow( 0.01, 1.0 / ( attackMS * maxiSettings::sampleRate * 0.001 ) );
}

void maxiEnv::setRelease(double releaseMS) {
    release = pow( 0.01, 1.0 / ( releaseMS * maxiSettings::sampleRate * 0.001 ) );
}

void maxiEnv::setSustain(double sustainL) {
    sustain = sustainL;
}

void maxiEnv::setDecay(double decayMS) {
    decay = pow( 0.01, 1.0 / ( decayMS * maxiSettings::sampleRate * 0.001 ) );
}

void maxiDyn::setAttack(double attackMS) {
    attack = pow( 0.01, 1.0 / ( attackMS * maxiSettings::sampleRate * 0.001 ) );
}

void maxiDyn::setRelease(double releaseMS) {
    release = pow( 0.01, 1.0 / ( releaseMS * maxiSettings::sampleRate * 0.001 ) );
}

void maxiDyn::setThreshold(double thresholdI) {
    threshold = thresholdI;
}

void maxiDyn::setRatio(double ratioF) {
    ratio = ratioF;
}


double convert::mtof(int midinote) {
	
	return mtofarray[midinote];
}


template<> void maxiEnvelopeFollower::setAttack(double attackMS) {
    attack = pow( 0.01, 1.0 / ( attackMS * maxiSettings::sampleRate * 0.001 ) );
}

template<> void maxiEnvelopeFollower::setRelease(double releaseMS) {
    release = pow( 0.01, 1.0 / ( releaseMS * maxiSettings::sampleRate * 0.001 ) );    
}

double pitchRatios[256]= {0.0006517771980725,0.0006905338959768,0.0007315951515920, 0.0007750981021672, 0.0008211878011934, 0.0008700182079338, 0.0009217521874234, 0.0009765623835847, 0.0010346318595111, 0.0010961542138830, 0.0011613349197432, 0.0012303915573284, 0.0013035543961450, 0.0013810677919537, 0.0014631903031841, 0.0015501962043345, 0.0016423756023869, 0.0017400364158675, 0.0018435043748468, 0.0019531247671694, 0.0020692637190223, 0.0021923084277660, 0.0023226698394865, 0.0024607831146568, 0.0026071087922901, 0.0027621355839074, 0.0029263808391988, 0.0031003924086690, 0.0032847514376044, 0.0034800728317350, 0.0036870087496936, 0.0039062497671694, 0.0041385274380445, 0.0043846168555319, 0.0046453396789730, 0.0049215662293136, 0.0052142175845802, 0.0055242711678147, 0.0058527616783977, 0.0062007848173380, 0.0065695028752089, 0.0069601456634700, 0.0073740174993873, 0.0078124995343387, 0.0082770548760891, 0.0087692337110639, 0.0092906802892685, 0.0098431324586272, 0.0104284351691604, 0.0110485423356295, 0.0117055233567953, 0.0124015696346760, 0.0131390057504177, 0.0139202913269401, 0.0147480349987745, 0.0156249990686774, 0.0165541097521782, 0.0175384692847729, 0.0185813605785370, 0.0196862649172544, 0.0208568722009659, 0.0220970865339041, 0.0234110467135906, 0.0248031392693520, 0.0262780115008354, 0.0278405826538801, 0.0294960699975491, 0.0312499981373549, 0.0331082195043564, 0.0350769385695457, 0.0371627211570740, 0.0393725298345089, 0.0417137444019318, 0.04419417306780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
    inverse = false;
    gain = 1;
    
    maxiKick::envelope.setAttack(0);
    maxiKick::setPitch(200);
    maxiKick::envelope.setDecay(1);
    maxiKick::envelope.setSustain(1);
    maxiKick::envelope.setRelease(500);
    maxiKick::envelope.holdtime=1;
    maxiKick::envelope.trigger=0;
    
};

double maxiKick::play(){
    
    envOut=envelope.adsr(1.,envelope.trigger);
    
    if (inverse) {
        
        envOut=fabs(1-envOut);
        
    }
    
    output=kick.sinewave(pitch*envOut)*envOut;
    
    if (envelope.trigger==1) {
        envelope.trigger=0;
    }
    
    if (useDistortion) {
        
        output=distort.fastAtanDist(output, distortion);
    }
    
    if (useFilter) {
        
        output=filter.lores(output, cutoff, resonance);
        
    }
    
    if (useLimiter) {
        
        if (output*gain > 1) {
            
            return 1.;
            
        } else if (output*gain < -1) {
            
            return -1.;
            
        } else {
            
            return output*gain;
            
        }
        
        
        
    } else {
        
        return output*gain;
        
    }
};

void maxiKick::setRelease(double release) {
    
    envelope.setRelease(release);
    
}

void maxiKick::setPitch(double newPitch) {
    
    pitch=newPitch;
    
}

void maxiKick::trigger() {
    
    envelope.trigger=1;
    
}

maxiSnare::maxiSnare()
{
    output = 0;
    outputD = 0;
    useDistortion = false;
    useLimiter = false;
    useFilter = true;
    distortion = 0;
    inverse = false;
    gain = 1;
    
    maxiSnare::envelope.setAttack(0);
    maxiSnare::setPitch(800);
    maxiSnare::envelope.setDecay(20);
    maxiSnare::envelope.setSustain(0.05);
    maxiSnare::envelope.setRelease(300);
    maxiSnare::envelope.holdtime=1;
    maxiSnare::envelope.trigger=0;
    
};

double maxiSnare::play(){
    
    envOut=envelope.adsr(1.,envelope.trigger);
    
    if (inverse) {
        
        envOut=fabs(1-envOut);
        
    }
    
    output=(tone.triangle(pitch*(0.1+(envOut*0.85)))+noise.noise())*envOut;
    
    if (envelope.trigger==1) {
        envelope.trigger=0;
    }
    
    if (useDistortion) {
        
        output=distort.fastAtanDist(output, distortion);
    }
    
    if (useFilter) {
        
        output=filter.lores(output, cutoff, resonance);
        
    }
    
    if (useLimiter) {
        
        if (output*gain > 1) {
            
            return 1.;
            
        } else if (output*gain < -1) {
            
            return -1.;
            
        } else {
            
            return output*gain;
            
        }
        
        
        
    } else {
        
        return output*gain;
        
    }
    
};

void maxiSnare::setRelease(double release) {
    
    envelope.setRelease(release);
    
}

void maxiSnare::setPitch(double newPitch) {
    
    pitch=newPitch;
    
}

void maxiSnare::trigger() {
    
    envelope.trigger=1;
    
}

maxiHats::maxiHats()
{
    output = 0;
    outputD = 0;
    useDistortion = false;
    useLimiter = false;
    useFilter = false;
    distortion = 0;
    inverse = false;
    gain = 1;
    
    maxiHats::envelope.setAttack(0);
    maxiHats::setPitch(12000);
    maxiHats::envelope.setDecay(20);
    maxiHats::envelope.setSustain(0.1);
    maxiHats::envelope.setRelease(300);
    maxiHats::envelope.holdtime=1;
    maxiHats::envelope.trigger=0;
    maxiHats::filter.setCutoff(8000);
    maxiHats::filter.setResonance(1);
    
};

double maxiHats::play(){
    
    envOut=envelope.adsr(1.,envelope.trigger);
    
    if (inverse) {
        
        envOut=fabs(1-envOut);
        
    }
    
    output=(tone.sinebuf(pitch)+noise.noise())*envOut;
    
    if (envelope.trigger==1) {
        envelope.trigger=0;
    }
    
    if (useDistortion) {
        
        output=distort.fastAtanDist(output, distortion);
    }
    
    if (useFilter) {
        
        output=filter.play(output, 0., 0., 1., 0.);
        
    }
    
    if (useLimiter) {
        
        if (output*gain > 1) {
            
            return 1.;
            
        } else if (output*gain < -1) {
            
            return -1.;
            
        } else {
            
            return output*gain;
            
        }
        
        
        
    } else {
        
        return output*gain;
        
    }
    
};

void maxiHats::setRelease(double release) {
    
    envelope.setRelease(release);
    
}

void maxiHats::setPitch(double newPitch) {
    
    pitch=newPitch;
    
}

void maxiHats::trigger() {
    
    envelope.trigger=1;
    
}



maxiClock::maxiClock() {
    
    playHead=0;
    currentCount=0;
    lastCount=0;
    bpm=120;
    ticks=1;
    maxiClock::setTempo(bpm);
    
}


void maxiClock::ticker() {
    
    tick=false;
    currentCount=floor(timer.phasor(bps));//this sets up a metronome that ticks n times a second
    
    if (lastCount!=currentCount) {//if we have a new timer int this sample,
        
        tick=true;
        playHead++;//iterate the playhead
        
    }
    
}


void maxiClock::setTempo(double bpmIn) {
    
    bpm=bpmIn;
    bps=(bpm/60.)*ticks;
}


void maxiClock::setTicksPerBeat(int ticksPerBeat) {
    
    ticks=ticksPerBeat;
    maxiClock::setTempo(bpm);
    
}

maxiSampler::maxiSampler()
{
    originalPitch=67;
    outputD = 0;
    useDistortion = false;
    useLimiter = false;
    useFilter = false;
    distortion = 0;
    inverse = false;
    gain = 1;
    currentVoice=0;
    sustain = true;

    maxiSampler::voices=32;
    maxiSampler::currentVoice=0;
    
    for (int i=0;i<voices;i++) {
        
        maxiSampler::envelopes[i].setAttack(0);
        maxiSampler::envelopes[i].setDecay(1);
        maxiSampler::envelopes[i].setSustain(1.);
        maxiSampler::envelopes[i].setRelease(2000);
        maxiSampler::envelopes[i].holdtime=1;
        maxiSampler::envelopes[i].trigger=0;
        maxiSampler::envOut[i]=0;
        maxiSampler::pitch[i]=0;
        maxiSampler::outputs[i]=0;
        
        
    }
}

void maxiSampler::setNumVoices(int numVoices) {
    
    voices=numVoices;
    
}

double maxiSampler::play() {
    
    output=0;
    
    for (int i=0;i<voices;i++) {
        
        envOut[i]=envelopes[i].adsr(envOutGain[i],envelopes[i].trigger);
        
        if (envOut[i]>0.) {
            outputs[i]=samples[i].play(pitchRatios[(int)pitch[i]+originalPitch]*((1./samples[i].length)*maxiSettings::sampleRate),0,samples[i].length)*envOut[i];
            output+=outputs[i]/voices;
            
            if (envelopes[i].trigger==1 && !sustain) {
                envelopes[i].trigger=0;
                
            }
            
        }
        
    } return output;
    
}

void maxiSampler::load(string inFile, bool setall) {
    
    if (setall) {
        for (int i=0;i<voices;i++) {
            
            samples[i].load(inFile);
            
        }
        
    } else {
        
        samples[currentVoice].load(inFile);
        
    }
    
    
}

void maxiSampler::setPitch(double pitchIn, bool setall) {
    
    if (setall) {
        for (int i=0;i<voices;i++) {
            
            pitch[i]=pitchIn;
            
        }
        
    } else {
        
        pitch[currentVoice]=pitchIn;
        
    }
    
}

void maxiSampler::midiNoteOn(double pitchIn, double velocity, bool setall) {
    
    if (setall) {
        for (int i=0;i<voices;i++) {
            
            pitch[i]=pitchIn;
            
        }
        
    } else {
        
        pitch[currentVoice]=pitchIn;
        envOutGain[currentVoice]=velocity/128;
        
    }
    
}

void maxiSampler::midiNoteOff(double pitchIn, double velocity, bool setall) {
    
    
    for (int i=0;i<voices;i++){
        
        if (pitch[i]==pitchIn) {
            
            envelopes[i].trigger=0;
            
        }
        
    }
}


void maxiSampler::setAttack(double attackD, bool setall) {
    
    if (setall) {
        
        for (int i=0;i<voices;i++) {
            
            envelopes[i].setAttack(attackD);
            
        }
        
    } else {
        
        envelopes[currentVoice].setAttack(attackD);
        
        
    }
    
    
}

void maxiSampler::setDecay(double decayD, bool setall) {
    
    if (setall) {
        
        for (int i=0;i<voices;i++) {
            
            envelopes[i].setDecay(decayD);
            
        }
        
    } else {
        
        envelopes[currentVoice].setDecay(decayD);
        
        
    }
    
    
}

void maxiSampler::setSustain(double sustainD, bool setall) {
    
    if (setall) {
        
        for (int i=0;i<voices;i++) {
            
            envelopes[i].setSustain(sustainD);
            
        }
        
    } else {
        
        envelopes[currentVoice].setSustain(sustainD);
        
        
    }
    
    
}

void maxiSampler::setRelease(double releaseD, bool setall) {
    
    if (setall) {
        
        for (int i=0;i<voices;i++) {
            
            envelopes[i].setRelease(releaseD);
            
        }
        
    } else {
        
        envelopes[currentVoice].setRelease(releaseD);
        
        
    }
    
    
}

void maxiSampler::setPosition(double positionD, bool setall){
    
    if (setall) {
        
        for (int i=0;i<voices;i++) {
            
            samples[i].setPosition(positionD);
            
        }
        
    } else {
        
        samples[currentVoice].setPosition(positionD);
        
        
    }
    
    
}

void maxiSampler::trigger() {
    
    envelopes[currentVoice].trigger=1;
    samples[currentVoice].trigger();
    currentVoice++;
    currentVoice=currentVoice%voices;
    
}
